mbodis/epaper-chess-puzzles/res/box-cover-1.png

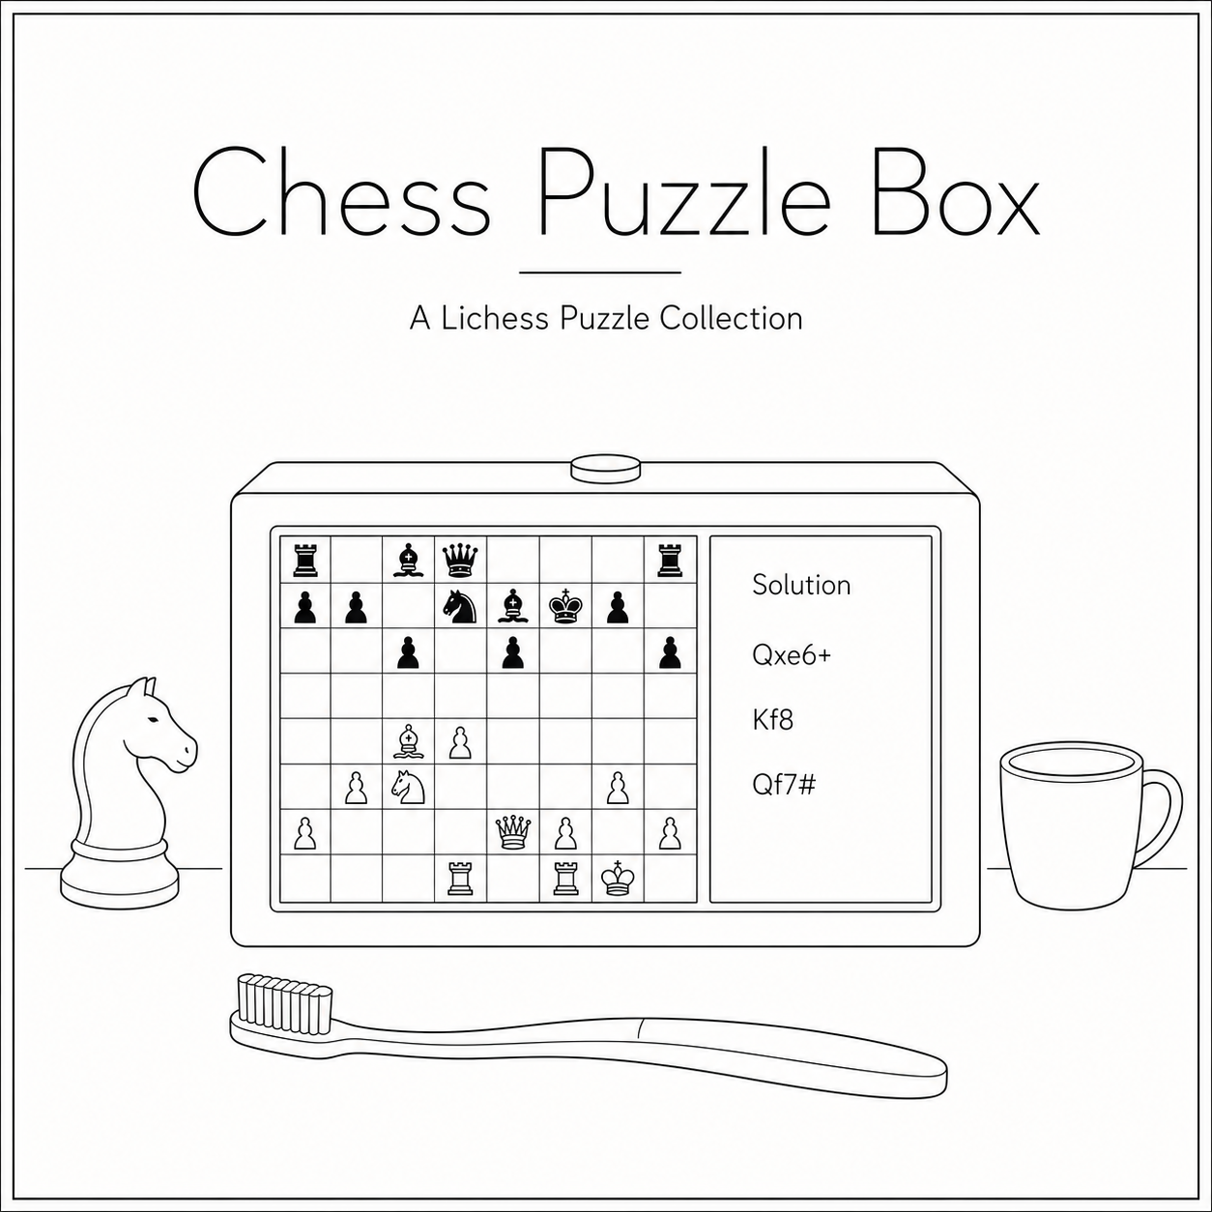
res/box-cover-1.png
