mbodis/epaper-chess-puzzles/ImageData.c

#include "ImageData.h"

const unsigned char white[128] = {
255,255,255,255,254,255,189,239,183,183,239,123,255,254,255,255,237,223,187,190,255,253,255,251,221,191,221,223,255,247,119,127,238,253,255,239,255,239,253,251,183,127,111,127,253,253,255,239,255,223,221,251,238,247,127,223,191,255,238,253,251,110,251,247,255,251,255,191,183,191,110,253,253,255,255,239,223,219,187,191,251,255,255,246,255,187,119,127,183,255,223,223,255,109,254,253,237,255,119,239,255,255,255,123,223,87,187,255,253,254,255,221,247,255,221,255,223,237,247,187,253,191,127,239,255,247,254,255,
};

const unsigned char black[128] = {
170,42,169,73,69,73,21,37,41,36,162,74,74,82,84,161,40,164,137,42,133,21,82,149,84,168,138,72,37,5,36,165,72,180,169,18,42,69,18,169,81,40,170,34,21,74,69,73,162,17,40,42,85,85,75,69,136,162,36,41,37,21,82,146,84,168,132,170,34,69,85,5,149,41,18,104,73,74,73,21,148,145,84,162,34,74,37,41,84,169,82,82,18,36,137,9,165,74,82,170,82,146,148,164,36,36,73,9,74,170,164,165,41,72,137,42,68,37,42,145,41,84,164,74,
};

const unsigned char black_bishop_b[128] = {
10,160,20,138,84,21,201,84,34,202,164,137,85,20,74,82,8,164,37,36,85,72,40,74,34,36,21,81,84,168,169,36,18,144,74,149,165,32,132,72,40,192,5,37,146,65,129,84,74,128,2,69,164,130,129,40,18,128,1,74,169,0,1,36,36,128,1,82,74,128,0,132,34,128,3,85,84,160,2,40,18,85,181,69,164,138,68,148,42,96,2,73,144,128,1,36,66,0,0,5,48,0,0,4,64,1,0,13,48,1,64,4,85,85,85,90,42,170,91,106,74,169,36,145,148,66,146,74,
};

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
};
