mbodis/epaper-chess-puzzles/ChessPuzzle.h

#ifndef CHESSPUZZLE_H
#define CHESSPUZZLE_H

/* display version selection */
// #define USE_EPAPER_V2  // Uncomment this line to use 4.2" e-paper V2 display

/* display constants (same for both original and V2) */
#define EPAPER_WIDTH  400
#define EPAPER_HEIGHT 300

/* display */
#include "DEV_Config.h"
#include "EPD.h"
#include "GUI_Paint.h"
#include "imagedata.h"
#include <stdlib.h>
#include <string.h>

#include <Arduino.h>
#include "ChessBoard.h"

class ChessPuzzle {

public:
  // lichess puzzle id e.g. 00sHx
  char* id = new char[10];

  // e.g. q3k1nr/1pp1nQpp/3p4/1P2p3/4P3/B1PP1b2/B5PP/5K2 b k - 0 17
  char* fenNotation = new char[100];

  // e.g. e8d7 a2e6 d7d8 f7f8
  char* solution = new char[100];

  // boolean of next move
  bool whiteIsOnTheMove = false;

  // e.g. kqKQ
  // k - black king side
  // q - black queen side
  // K - white king side
  // Q - white queen side
  char* castlingAvailability = new char[10];

  // e.g. e3, or - when not possible
  char* enPassant = new char[20];

  long puzzleCounter = 0;
  bool isMessage = false;

  ChessBoard chessBoard;

  ChessPuzzle();
  void init();
  void printToLog();
  void drawChessboard();
  void drawSolution();
  char* convertSolutionToSan(); // Convert entire solution string from UCI to SAN

private:
  // Renders the current puzzle (welcome / congratulations / chessboard
  // + metadata) into the given full-screen image buffer.
  // Shared between drawChessboard() and drawSolution() so the solution
  // view can include the chessboard as background for V2 partial refresh.
  void renderChessboardImage(UBYTE *image);
};

#endif  // CHESSPUZZLE_H
