mbodis/epaper-chess-puzzles/ImageData.h

#ifndef _IMAGEDATA_H_
#define _IMAGEDATA_H_

extern const unsigned char black[128];
extern const unsigned char white[128];

extern const unsigned char black_bishop_b[128];
extern const unsigned char black_bishop_w[128];
extern const unsigned char black_king_b[128];
extern const unsigned char black_king_w[128];
extern const unsigned char black_knight_b[128];
extern const unsigned char black_knight_w[128];
extern const unsigned char black_pawn_b[128];
extern const unsigned char black_pawn_w[128];
extern const unsigned char black_queen_b[128];
extern const unsigned char black_queen_w[128];
extern const unsigned char black_rook_b[128];
extern const unsigned char black_rook_w[128];

extern const unsigned char white_bishop_b[128];
extern const unsigned char white_bishop_w[128];
extern const unsigned char white_king_b[128];
extern const unsigned char white_king_w[128];
extern const unsigned char white_knight_b[128];
extern const unsigned char white_knight_w[128];
extern const unsigned char white_pawn_b[128];
extern const unsigned char white_pawn_w[128];
extern const unsigned char white_queen_b[128];
extern const unsigned char white_queen_w[128];
extern const unsigned char white_rook_b[128];
extern const unsigned char white_rook_w[128];

#endif
